dciliberti/DHT22_5sensor/example/sensor1.png

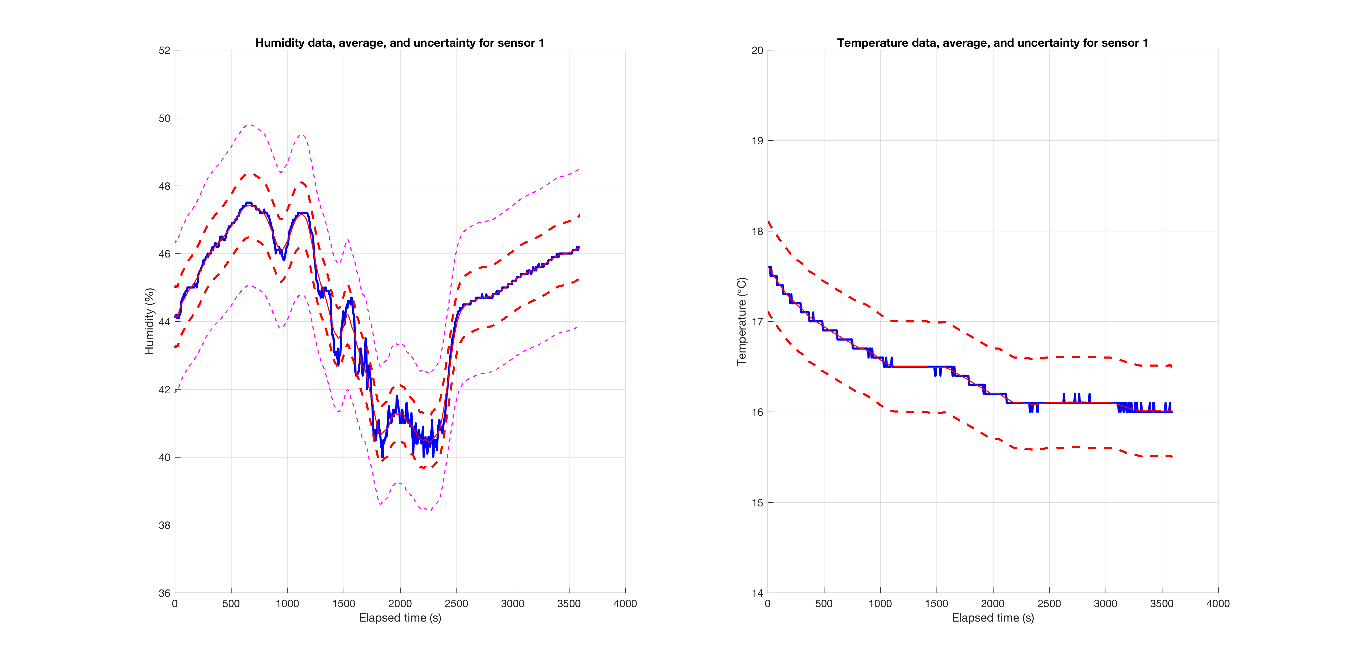
example/sensor1.png
