dciliberti/DHT22_5sensor/example/sensor5.png

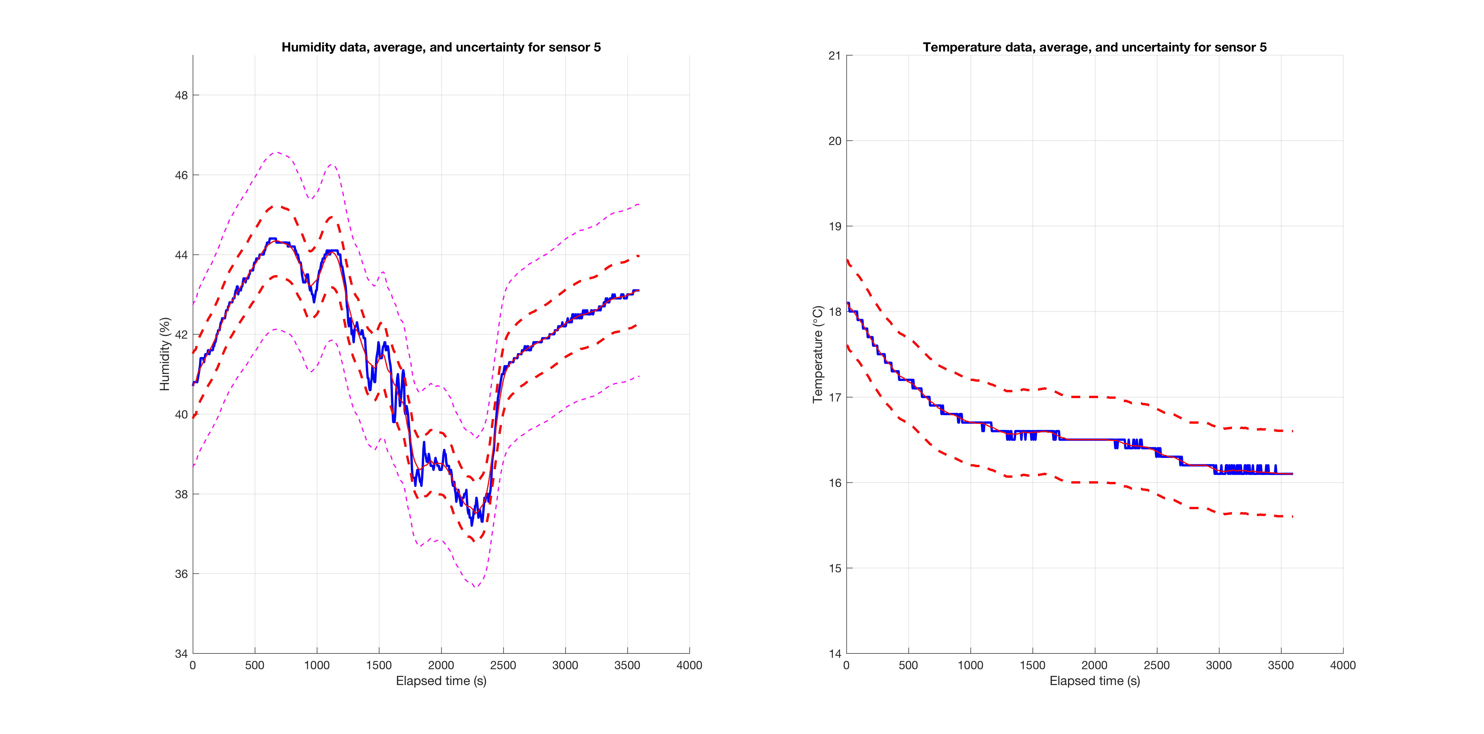
example/sensor5.png
